ianmaclarty/ik/1.2/photos/case_top.png

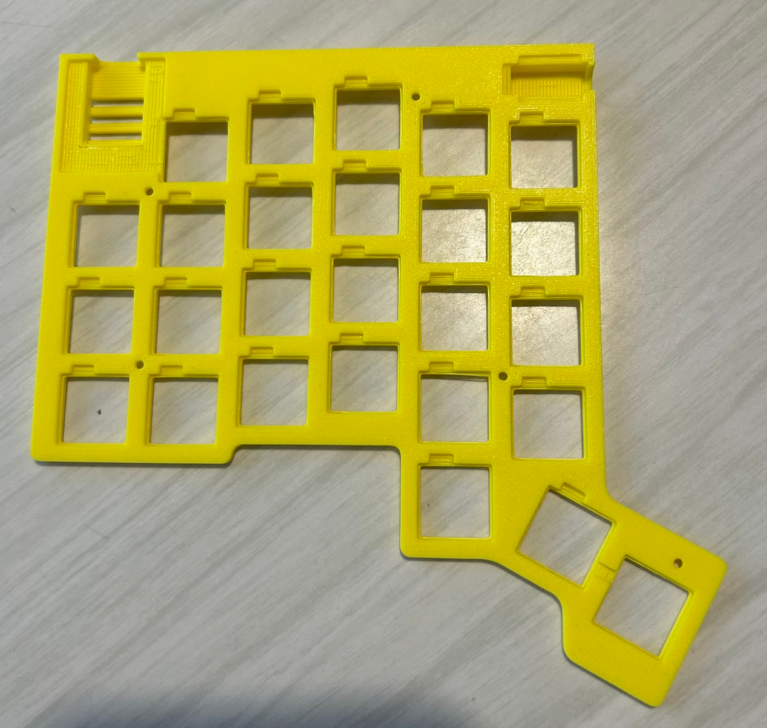
1.2/photos/case_top.png
