ianmaclarty/ik/1.2/photos/mcu_soldered.png

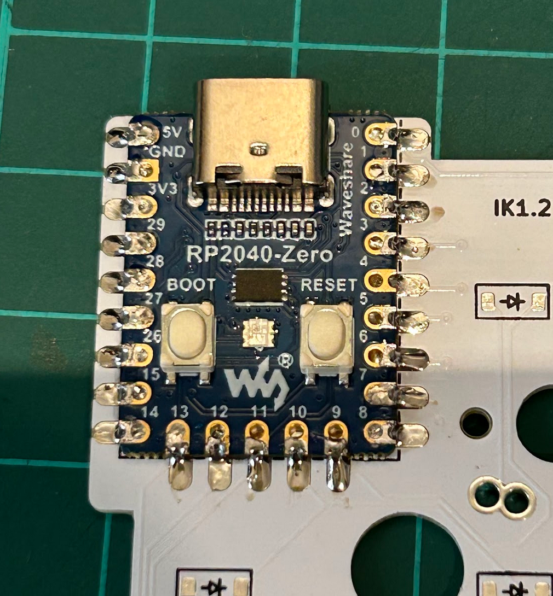
1.2/photos/mcu_soldered.png
