ianmaclarty/ik/1.2/photos/ready_for_final_assembly.png

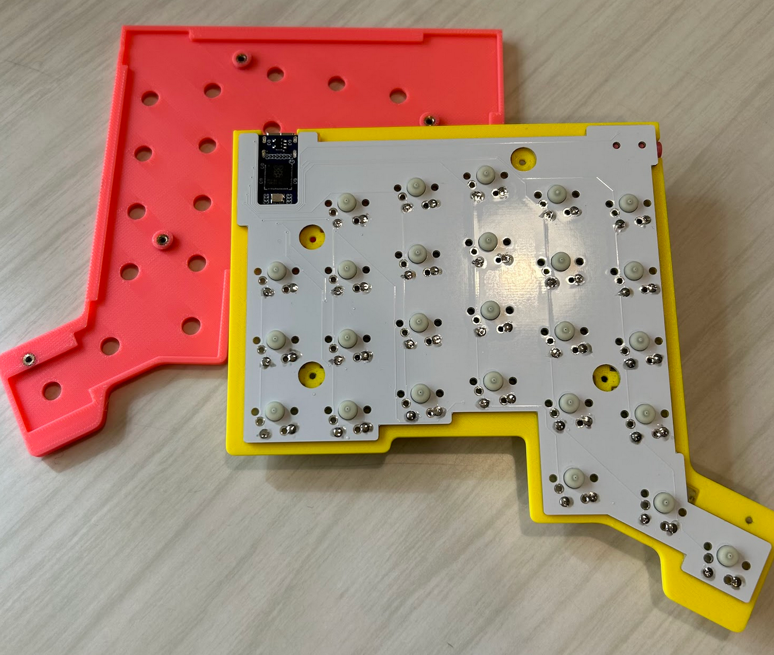
1.2/photos/ready_for_final_assembly.png
